riban-bw/modular/firmware/brain/src/main.cpp

/* riban modular

  Copyright 2023-2024 riban ltd <info@riban.co.uk>

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
  Provides firmware for Brain controller board implemented on STM32F103C microcontrollers using arduino framework.
*/

#include "global.h"   // Common riban modular code
#include <STM32CAN.h> // Provides CAN bus interface
#include "ws2812.hpp"    // Implements WS2812 LED functionality
#include "switches.hpp"  // Implements switch / button functionality
#include "adcs.hpp"      // Implements ADC functionality

#define MAX_PANELS 63
#define MAX_USART_MSG_LEN 12

struct PANEL_T
{
  uint32_t type = 0; // Panel type
  uint32_t uuid0 = 0; // Panel UID [0:31]
  uint32_t uuid1 = 0; // Panel UID [32:63]
  uint32_t uuid2 = 0; // Panel UID [64:95]
  uint32_t version = 0; // Panel firmware version
  uint8_t switches[32];
  uint16_t adcs[16];
  uint32_t lastUpdate = 0; // Time of last CAN message
};


// Global variables
static volatile uint32_t now = 0; // Uptime in ms (49 day roll-over)
uint8_t numPanels = 0;            // Quantity of detected and configured panels
uint8_t usartRxBuffer[MAX_USART_MSG_LEN]; // Buffer holding data received from USART
uint8_t usartRxLen = 0;           // Length of usartRxBuffer
static CAN_message_t canMsg;      // CAN message object used to send and receive
PANEL_T panels[MAX_PANELS];       // Array of panel configurations (0 used for detection)
uint8_t detecting = RUN_MODE_INIT; // Panel detection mode
HardwareSerial Serial1(PA10, PA9); // USART for communication with host

// Forward declarations
void processUsart();
void usartTx(uint8_t*, uint8_t);

void SystemClock_Config(void)
{
  RCC_OscInitTypeDef RCC_OscInitStruct = {};
  RCC_ClkInitTypeDef RCC_ClkInitStruct = {};
  RCC_PeriphCLKInitTypeDef PeriphClkInit = {};

  /* Initializes the CPU, AHB and APB busses clocks */
  RCC_OscInitStruct.OscillatorType = RCC_OSCILLATORTYPE_HSE;
  RCC_OscInitStruct.HSEState = RCC_HSE_ON;
  RCC_OscInitStruct.HSEPredivValue = RCC_HSE_PREDIV_DIV1;
  RCC_OscInitStruct.HSIState = RCC_HSI_ON;
  RCC_OscInitStruct.PLL.PLLState = RCC_PLL_ON;
  RCC_OscInitStruct.PLL.PLLSource = RCC_PLLSOURCE_HSE;
  RCC_OscInitStruct.PLL.PLLMUL = RCC_PLL_MUL9;
  if (HAL_RCC_OscConfig(&RCC_OscInitStruct) != HAL_OK) {
    Error_Handler();
  }

  /* Initializes the CPU, AHB and APB busses clocks */
  RCC_ClkInitStruct.ClockType = RCC_CLOCKTYPE_HCLK | RCC_CLOCKTYPE_SYSCLK
                                | RCC_CLOCKTYPE_PCLK1 | RCC_CLOCKTYPE_PCLK2;
  RCC_ClkInitStruct.SYSCLKSource = RCC_SYSCLKSOURCE_PLLCLK;
  RCC_ClkInitStruct.AHBCLKDivider = RCC_SYSCLK_DIV1;
  RCC_ClkInitStruct.APB1CLKDivider = RCC_HCLK_DIV2;
  RCC_ClkInitStruct.APB2CLKDivider = RCC_HCLK_DIV1;

  if (HAL_RCC_ClockConfig(&RCC_ClkInitStruct, FLASH_LATENCY_2) != HAL_OK) {
    Error_Handler();
  }

  PeriphClkInit.PeriphClockSelection = RCC_PERIPHCLK_ADC | RCC_PERIPHCLK_USB;
  PeriphClkInit.AdcClockSelection = RCC_ADCPCLK2_DIV6;
  PeriphClkInit.UsbClockSelection = RCC_USBCLKSOURCE_PLL_DIV1_5;
  if (HAL_RCCEx_PeriphCLKConfig(&PeriphClkInit) != HAL_OK) {
    Error_Handler();
  }
}

void setup()
{
  initLeds();
  initSwitches();
  initAdcs();

  Can1.setRxBufferSize(16);
  Can1.setTxBufferSize(16);
  Can1.begin(CAN_SPEED);
  canMsg.id = CAN_MSG_BROADCAST;
  canMsg.dlc = 1;
  canMsg.ide = IDExt;
  canMsg.data.bytes[0] = CAN_BROADCAST_RESET;

  Serial1.begin(1152000); // USART1 used for comms to host
  uint8_t data[] = {HOST_CMD, HOST_CMD_RESET, 0};
  usartTx(data, 2); // Send reset to host
  if (!Can1.write(canMsg))
    ; //CAN Tx RESET failed
}

void loop()
{
  static uint32_t lastNow = 0;
  static uint32_t nextRefresh = 0;
  static uint32_t nextSec = 0;
  static uint32_t next10ms = 0;
  static uint32_t startDetectTime = 0;
  static uint32_t nextSensorScan = 0;
  static uint8_t txBuffer[12];

  now = millis();
  if (lastNow != now)
  {
    // 1ms actions
    lastNow = now;
    if (now > nextRefresh)
    {
      nextRefresh = now + REFRESH_RATE;
      processLeds();
      if (now > nextSec)
      {
        // 1s actions
        nextSec = now + 1000;
        //!@todo Scan panels for timeouts, remove missing panels
      }
    }
    if (detecting == RUN_MODE_RUN) {
      // Run mode
      if (now > next10ms)
      {
        // 10ms actions
        next10ms = now + 10;
      }

      // Process local (Brain) sensors
      if (now > nextSensorScan) {
        uint32_t adcChanged = processAdcs(now);
        uint8_t i = 0;
        while (adcChanged) {
          if (adcChanged & 0x01) {
            txBuffer[0] = 0;
            txBuffer[1] = CAN_MSG_ADC | 0x10;
            txBuffer[2] = i;
            txBuffer[3] = adcs[i].value >> 8;
            txBuffer[4] = adcs[i].value & 8;
            usartTx(txBuffer, 5);
          }
          adcChanged >>= 1;
          ++i;
        }

        for (uint8_t i = 0; i < switchCount; ++i) {
          if (processSwitch(i, now)) {
            txBuffer[0] = 0;
            txBuffer[1] = CAN_MSG_SWITCH | 0x10;
            txBuffer[2] = 3;
            txBuffer[4] = i;
            txBuffer[5] = switches[i].state;
            usartTx(txBuffer, 6);
          }
        }
        nextSensorScan = now + 15;
      }

    } else {
      if (now > startDetectTime + 500)
      {
        // Detection timed out so enter run mode
        canMsg.ide = IDExt;
        canMsg.id = CAN_MSG_BROADCAST;
        canMsg.data.bytes[0] = CAN_BROADCAST_RUN;
        canMsg.dlc = 1;
        if (!Can1.write(canMsg))
          ; //CAN Tx DETECT END failed"
        detecting = RUN_MODE_RUN;
      }
    }
  }

  // Handle incoming CAN messages
  if (Can1.read(canMsg))
  {
    uint8_t panelId;
    if (canMsg.ide)
    {
      // Extended CAN message
      switch (canMsg.id & CAN_FILTER_ID_DETECT)
      {
      case CAN_MSG_DETECT_1:
        // At least one panel has requested to start detection
        if (detecting != RUN_MODE_RUN && detecting != RUN_MODE_READY) 
          break;
        startDetectTime = now;
        if (canMsg.dlc == 0)
        {
          canMsg.data.low = (canMsg.id & 0x00FFFFFF);
          panels[0].uuid0 = (canMsg.id && 0x00FFFFFF) << 8;
          canMsg.id = CAN_MSG_DETECT_1;
          canMsg.dlc = 4;
          if (!Can1.write(canMsg))
            ; //CAN Tx DETECT 1 failed"
          else
            detecting = RUN_MODE_PENDING_1;
        }
        break;
      case CAN_MSG_DETECT_2:
        if (detecting != RUN_MODE_PENDING_1)
          break;
        if (canMsg.dlc == 0)
        {
          canMsg.data.low = (canMsg.id & 0x00FFFFFF);
          panels[0].uuid0 |= (canMsg.id & 0x00FF0000) >> 16;
          panels[0].uuid1 = canMsg.id << 16;
          canMsg.id = CAN_MSG_DETECT_2;
          canMsg.dlc = 4;
          if (!Can1.write(canMsg))
            ; //CAN Tx DETECT 2 failed
          else
            detecting = RUN_MODE_PENDING_2;
        }
        break;
      case CAN_MSG_DETECT_3:
        if (detecting != RUN_MODE_PENDING_2)
          break;
        if (canMsg.dlc == 0)
        {
          canMsg.data.low = (canMsg.id & 0x00FFFFFF);
          panels[0].uuid1 |= (canMsg.id & 0x00FFFF00) >> 8;
          panels[0].uuid2 = canMsg.id << 24;
          canMsg.id = CAN_MSG_DETECT_3;
          canMsg.dlc = 4;
          if (!Can1.write(canMsg))
            ; //CAN Tx DETECT 3 failed
          else
            detecting = RUN_MODE_PENDING_3;
        }
        break;
      case CAN_MSG_DETECT_4:
        if (detecting != RUN_MODE_PENDING_3)
          break;
        if (canMsg.dlc == 0)
        {
          panels[0].uuid2 |= (canMsg.id & 0x00FFFFFF);
          // Search for existing panel config and first free panel id
          uint8_t firstFreeId = 0;
          numPanels = 0;
          for (panelId = 1; panelId < MAX_PANELS; ++panelId) {
            if (panels[panelId].type != 0)
              ++numPanels;
            else if (firstFreeId == 0)
              firstFreeId = panelId;
            if (panels[0].uuid0 == panels[panelId].uuid0 && panels[0].uuid1 == panels[panelId].uuid1 && panels[0].uuid2 == panels[panelId].uuid2)
              break;
          }
          if (panelId >= MAX_PANELS)
            if (firstFreeId)
              panelId = firstFreeId;
            else
              ; //!@todo Failed to get a free panel ID
          canMsg.data.low = ((canMsg.id & 0x00FFFFFF) << 8) | panelId;
          canMsg.id = CAN_MSG_DETECT_4;
          canMsg.dlc = 4;
          if (!Can1.write(canMsg))
            ; //CAN Tx DETECT 4 failed
          else
            detecting = RUN_MODE_PENDING_4;
        }
        break;
      case CAN_MSG_ACK_ID:
        if (detecting != RUN_MODE_PENDING_4)
          break;
        if (canMsg.dlc == 8)
        {
          panels[0].type = canMsg.data.low;
          panels[0].version = canMsg.data.high;
          panels[0].lastUpdate = now;
          panelId = canMsg.id & 0x3F;
          memcpy(panels[panelId], panels[0], sizeof(PANEL_T));
          // Inform host of new panel
          uint8_t data[23] = {0xFF, HOST_CMD_PNL_INFO, panelId};
          memcpy(data + 2, 20, panels[panelId]);
          usartTx(data, 23);
          detecting = RUN_MODE_READY;
        }
        break;
      }
    } else {
      // Send all standard CAN messages to host via USART
      uint8_t buffer[11];
      buffer[0] = canMsg.id >> 8;
      buffer[1] = canMsg.id & 0xff;
      uint8_t pnlId = canMsg.data.bytes[0];
      if (pnlId < MAX_PANELS)
        panels[pnlId].lastUpdate = now;
      memcpy(buffer + 2, canMsg.data.bytes, canMsg.dlc);
      usartTx(buffer, canMsg.dlc + 2);
    }
    digitalToggle(PC13); // toggle LED on each received CAN message
  }

  // Handle USART received bytes
  processUsart();
}

/** @brief  Process incoming USART COBS encoded messages, dispatching to CAN as required */
void processUsart() {
  int rxCount = 0;
  while(Serial1.available()) {
    usartRxBuffer[usartRxLen] = Serial1.read();
    if (usartRxBuffer[usartRxLen++] == 0) { // Found frame delimiter
      if (usartRxLen < 6)
        break; // Invalid or empty message
      // Decode COBS in usartRxBuffer (in place)
      uint8_t nextZero = usartRxBuffer[0];
      for (uint8_t i = 0; i < usartRxLen; ++i) {
        if (i == nextZero) {
          nextZero = i + usartRxBuffer[i];
          usartRxBuffer[i] = 0;
        }
      }
      // Check checksum
      uint8_t checksum = 0;
      for (uint8_t i = 1; i < usartRxLen - 1; ++i)
        checksum += usartRxBuffer[i];
      if (checksum) {
        usartRxLen = 0;
        return; // Checksum error
      }
      usartRxLen -= 2;

      // Data starts at usartRxBuffer[1]
      if (usartRxBuffer[1] == HOST_CMD) {
        // Host command, not CAN message
        uint8_t data[8];
        data[0] = HOST_CMD;
        switch (usartRxBuffer[2]) {
          case HOST_CMD_PNL_INFO:
            // Request all panels info
            data[1] = HOST_CMD_PNL_INFO;
            for (uint8_t i = 0; i < MAX_PANELS; ++i) {
              if (panels[i].type) {
                data[2] = i;
                data[3] = panels[i].type >> 24;
                data[4] = panels[i].type >> 16;
                data[5] = panels[i].type >> 8;
                data[6] = panels[i].type & 0xff;
                usartTx(data, 7);
              }
            }
            break;
          case HOST_CMD_RESET:
            canMsg.id = CAN_MSG_BROADCAST;
            canMsg.dlc = 1;
            canMsg.ide = IDExt;
            canMsg.data.bytes[0] = CAN_BROADCAST_RESET;
            break;
          case HOST_CMD_PNL_RUN:
            //!@todo Set all panels to run mode
            canMsg.id = CAN_MSG_BROADCAST;
            canMsg.dlc = 1;
            canMsg.ide = IDExt;
            canMsg.data.bytes[0] = CAN_BROADCAST_RUN;
            break;
          default:
            break;
        }
      } else {
        uint16_t canId = (usartRxBuffer[1] << 8) | usartRxBuffer[2];
        uint8_t pnlId = (canId >> 4) & 0b111111;
        if (pnlId == 0) {
          // RPi->Brain (unCANny) control
          switch (canId & CAN_MASK_OPCODE) {
            case CAN_MSG_LED:
              if (usartRxLen > 4) {
                setLedState(usartRxBuffer[3], usartRxBuffer[4]);
                if (usartRxLen > 7) {
                  setLedColour1(usartRxBuffer[3], usartRxBuffer[5], usartRxBuffer[6], usartRxBuffer[7]);
                  if (usartRxLen > 10) {
                    setLedColour2(usartRxBuffer[3], usartRxBuffer[8], usartRxBuffer[9], usartRxBuffer[10]);
                  }
                }
              }
              break;
            default:
              ;
          }
        } else {
          // Send CAN message
          canMsg.id = (usartRxBuffer[1] << 8) | usartRxBuffer[2];
          canMsg.ide = IDStd;
          canMsg.dlc = usartRxLen - 3; // Remove start, stop and checksum bytes
          memcpy(canMsg.data.bytes, usartRxBuffer + 3, canMsg.dlc);
          if (Can1.write(canMsg))
            ; // Error sending CAN message
        }
      }
      usartRxLen = 0;
    } else if (usartRxLen >= MAX_USART_MSG_LEN)
        usartRxLen = 0; // All CAN messages are shorter than this
  }
}

void usartTx(uint8_t* data, uint8_t len) {
  // Data buffer must be len + 1 to accommodate checksum
  data[len] = 0;
  for (uint8_t i = 0; i < len; ++i) {
    data[len] -= data[i];
  }
  uint8_t buffer[len + 3];
  uint8_t zPtr = 0;
  for (uint8_t i = 0; i < len + 1; ++i) {
    if (data[i]) {
      buffer[i + 1] = data[i];
    } else {
      buffer[zPtr] = i + 1 - zPtr;
      zPtr = i + 1;
    }
  }
  buffer[zPtr] = len + 2 - zPtr;
  buffer[len + 2] = 0;
  Serial1.write(buffer, len + 3);
}
