riban-bw/modular/firmware/rmcore/plugins/src/bogamrm.cpp

/*  riban modular
    Copyright 2023-2025 riban ltd <info@riban.co.uk>
    Derived from Bogaudio AMRM Copyright 2021 Matt Demanett

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
    Bogaudio ring and amplitude modulator module class implementation.
*/

#include "bogamrm.h" 
#include "global.h"

DEFINE_PLUGIN(BOGAMRM)

BOGAMRM::BOGAMRM() {
    m_info.description = "Bogaudio noise generator";
    m_info.polyInputs = {
        "modulator",
        "carrier",
        "rectify",
        "wet"
        };
    m_info.polyOutputs = {
        "output",
        "rectify output"
    };
    m_info.params = {
        "rectify",
        "drywet"
    };
}

void BOGAMRM::init() {
}

int BOGAMRM::process(jack_nframes_t frames) {
    for (uint8_t poly = 0; poly < m_poly; ++poly) {
        jack_default_audio_sample_t * modBuffer = (jack_default_audio_sample_t*)jack_port_get_buffer(m_input[BOGAMRM_INPUT_MODULATOR].m_port[poly], frames);
        jack_default_audio_sample_t * carBuffer = (jack_default_audio_sample_t*)jack_port_get_buffer(m_input[BOGAMRM_INPUT_CARRIER].m_port[poly], frames);
        jack_default_audio_sample_t * rectBuffer = nullptr;
        if (m_input[BOGAMRM_INPUT_RECTIFY].isConnected())
            rectBuffer = (jack_default_audio_sample_t*)jack_port_get_buffer(m_input[BOGAMRM_INPUT_RECTIFY].m_port[poly], frames);
        jack_default_audio_sample_t * wetBuffer = nullptr;
        if (m_input[BOGAMRM_INPUT_DRYWET].isConnected())
            wetBuffer = (jack_default_audio_sample_t*)jack_port_get_buffer(m_input[BOGAMRM_INPUT_DRYWET].m_port[poly], frames);
        jack_default_audio_sample_t * outBuffer = (jack_default_audio_sample_t*)jack_port_get_buffer(m_output[BOGAMRM_OUTPUT_OUT].m_port[poly], frames);
        jack_default_audio_sample_t * rectOutBuffer = (jack_default_audio_sample_t*)jack_port_get_buffer(m_output[BOGAMRM_OUTPUT_RECTIFY].m_port[poly], frames);
        for (jack_nframes_t frame = 0; frame < frames; ++frame) {
            float rectify = m_param[BOGAMRM_PARAM_RECTIFY].getValue();
            if (rectBuffer) {
                rectify = clamp(rectify + rectBuffer[frame] / 10.0f, 0.0f, 1.0f);
            }
            rectify = 1.0f - rectify;
        
            float depth = m_param[BOGAMRM_PARAM_DRYWET].getValue();
            if (wetBuffer) {
                depth = clamp(depth + wetBuffer[frame] / 10.0f, 0.0f, 1.0f);
            }
        
            float modulator = modBuffer[frame];
            if (rectify < 1.0f) {
                rectify *= -5.0f;
                if (modulator < rectify) {
                    modulator = rectify - (modulator - rectify);
                }
            }
            rectOutBuffer[frame] = modulator;
        
            modulator *= depth;
            modulator += (1.0f - depth) * 5.0f;
            outBuffer[frame] = m_saturator.next(modulator * carBuffer[frame] * 0.2f);
        }
    }
    return 0;
}
