riban-bw/modular/firmware/rmcore/include/moduleManager.h

/*  riban modular
    Copyright 2023-2025 riban ltd <info@riban.co.uk>

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
    Module manager class header.
*/

#pragma once

#include "global.h"
#include "module.hpp"
#include <map> // Provides std::map
#include <string> // Provides std::string

class ModuleManager {
    public:

        /** @brief  Get the module manager singleton object
            @retval static ModuleManager Reference to the module manager object
        */
        static ModuleManager& get();

        /** @brief  Get list of running modules
            @retval std::map<const std::string, Module*>> Map of module UUIDs
        */
        const std::map<const std::string, Module*>& getModules();

        /** @brief  Get pointer to module
            @param  uuid UUID of the module
            @retval Module* Pointer to module or NULL if not found
        */
        Module* getModule(std::string uuid);

        /** @brief  Get list of available modules that may be instantiated
            @retval vector List of plugin names
        */
        std::vector<std::string> getAvailableModules();

        /** @brief  Add a module to the graph
            @param  type Module type
            @param  uuid Module UUID
            @retval Module* Pointer to module or null on failure
        */
        Module* addModule(const std::string& type, const std::string& uuid);

        /** @brief  Remove a module from the graph
            @param  type Module type
            @param  uuid UUID of the panel/module
            @retval bool True on success
        */
        bool removeModule(const std::string& uuid);

        /** @brief  Remove all modules from the graph
            @retval bool True on success
        */
        bool removeAll();

        /** @brief  Set value of a module parameter 
            @param  module  Module UUID
            @param  param   Index of parameter
            @param  value   Normalised value
            @retval bool    True on success
        */
        bool setParam(const std::string& uuid, uint32_t param, float value);

        /** @brief  Get value of a module parameter
            @param  module  Module UUID
            @param  param   Index of parameter
            @retval float   Normalised value
        */
        float getParam(const std::string& uuid, uint32_t param);

        /** @brief  Get name of a module parameter
            @param  module  Module UUID
            @param  param   Index of parameter
            @retval const std::string& Name or "" if invalid parameter
        */
        const std::string& getParamName(const std::string& uuid, uint32_t param);

        /** @brief  Get quantity of module parameters
            @param  module  Module UUID
            @retval uint32_t Quantity of parameters or 0 if invalid module
        */
        uint32_t getParamCount(const std::string& uuid);

        /** @brief  Get the next LED that has changed state since last call
            @param  uuid Module UUID
            @retval uint8_t Index of dirty LED or 0xff if none found
        */
        uint8_t getDirtyLed(const std::string& uuid);

        /** @brief  Get LED state
            @param  uuid Module UUID
            @param  led LED index
            @retval LED* Pointer to LED state structure or null if invalid uuid or index
        */
        LED* getLedState(const std::string& uuid, uint8_t led);

        /** @brief  Set polyphony
            @param  poly    Quantity of concurrent voices
        */
        void setPolyphony(uint8_t poly);

    private:
        uint8_t m_poly = 1;
        std::map<const std::string, Module*> m_modules; // Map of module pointers, indexed by uuid
};
