riban-bw/modular/firmware/rmcore/src/node.cpp

/*  riban modular
    Copyright 2023-2025 riban ltd <info@riban.co.uk>

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
    Node class implementation. Base class for all modules.
*/

#include "node.h"
#include <stdlib.h>
#include <cstring> // Provides std::memcpy
#include <stdio.h> // Provides sprintf

Node::~Node() {
    if (m_jackClient)
        if(jack_client_close(m_jackClient))
            fprintf(stderr, "Failed closing jack client\n");
}

void Node::_init(const std::string& uuid) {
    // Register with Jack server
    char* serverName = nullptr;
    char nameBuffer[128];
    jack_status_t status;
    jack_options_t options = JackNoStartServer;
    jack_port_t* port;

    sprintf(nameBuffer, "%s %s", m_info.name.c_str(), uuid.c_str());
    m_jackClient = jack_client_open(nameBuffer, options, &status, serverName);
    if (!m_jackClient) {
        fprintf(stderr, "Failed to open JACK client\n");
    }
    for (uint32_t i = 0; i < m_info.inputs.size(); ++i) {
        port = jack_port_register(m_jackClient, m_info.inputs[i].c_str(), JACK_DEFAULT_AUDIO_TYPE, JackPortIsInput, 0);
        if (port)
            m_input.push_back(port);
    }
    for (uint8_t poly = 0; poly < g_poly; ++poly) {
        for (uint32_t i = 0; i < m_info.polyInputs.size(); ++i) {
            sprintf(nameBuffer, "%s[%u]", m_info.polyInputs[i].c_str(), poly);
            port = jack_port_register(m_jackClient, nameBuffer, JACK_DEFAULT_AUDIO_TYPE, JackPortIsInput, 0);
            if (port)
                m_polyInput[poly].push_back(port);
        }
    }
    for (uint32_t i = 0; i < m_info.outputs.size(); ++i) {
        port = jack_port_register(m_jackClient, m_info.outputs[i].c_str(), JACK_DEFAULT_AUDIO_TYPE, JackPortIsOutput, 0);
        if (port)
            m_output.push_back(port);
    }
    for (uint8_t poly = 0; poly < g_poly; ++poly) {
        for (uint32_t i = 0; i < m_info.polyOutputs.size(); ++i) {
            sprintf(nameBuffer, "%s[%u]", m_info.polyOutputs[i].c_str(), poly);
            port = jack_port_register(m_jackClient, nameBuffer, JACK_DEFAULT_AUDIO_TYPE, JackPortIsOutput, 0);
            if (port)
                m_polyOutput[poly].push_back(port);
        }
    }
    for (uint32_t i = 0; i < m_info.params.size(); ++i) {
        m_param.push_back(0.0f);
    }
    if (m_info.midi) {
        port = jack_port_register(m_jackClient, "in", JACK_DEFAULT_MIDI_TYPE, JackPortIsInput, 0);
        if (port)
            m_midiIn = port;
    }
    init(); // Call derived class initalisaton
    jack_set_sample_rate_callback(m_jackClient, samplerateStatic, this);
    jack_set_process_callback(m_jackClient, processStatic, this);
    jack_activate(m_jackClient);
}

uint32_t Node::getNumInputs() {
    return m_input.size();
}

uint32_t Node::getNumOutputs() {
    return m_output.size();
}

float Node::getParam(uint32_t param) {
    if (param > m_param.size())
        return 0.0;
    return m_param[param];
}

bool Node::setParam(uint32_t param, float val) {
    if (param >= m_param.size())
        return false;
    m_param[param] = val;
    return true;
}

int Node::samplerateChange(jack_nframes_t samplerate) {
    if (samplerate ==0)
        return -1;
    m_samplerate = samplerate;
    return 0;
}
